AvansETI/SmartSensor/Software/Firmware/smart-sensor/include/SmartSensor.h

//
// Created by Patrick on 28/05/2020.
//

#ifndef SMART_SENSOR_SMARTSENSOR_H
#define SMART_SENSOR_SMARTSENSOR_H

// Use the XBEE Module on the Smart Sensor
#define USE_XBEE    0
#define S_IDLE      0
#define S_POLL      1
#define S_XBEE      2

#endif //SMART_SENSOR_SMARTSENSOR_H
