AvansETI/SmartSensor/Software/Firmware/Coordinator/include/config-template.h

#ifndef CONFIG_H_
#define CONFIG_H_

#define WIFI_SSID			""
#define WIFI_PASSWORD		""

#define MQTT_BROKER			""
#define MQTT_PORT			
#define MQTT_WEBSOCKET_PORT	
#define MQTT_TOPIC			""
#define PACKET_SIZE 		512
#endif
